ben-jacobson/bench_psu/IO.sch

## KiCad design IO.sch (2021-01-01)

Schematic: IO.sch

Parts:
C8, C13, C14, C16: 0.1uF
C9, C10, C11, C12: 1uF
R4, R5, R6, R7, R8, R11: 10K
R9, R10: 1K
SW2: CH1_Vadj
SW3: CH2_Vadj
U5: 74HC14
U7: 4013

Notes on the sheet:
CH1 Voltage Adjustment - Rotary Encoder
CH2 Voltage Adjustment - Rotary Encoder
