ben-jacobson/bench_psu/MCU.sch

## KiCad design MCU.sch (2021-01-09)

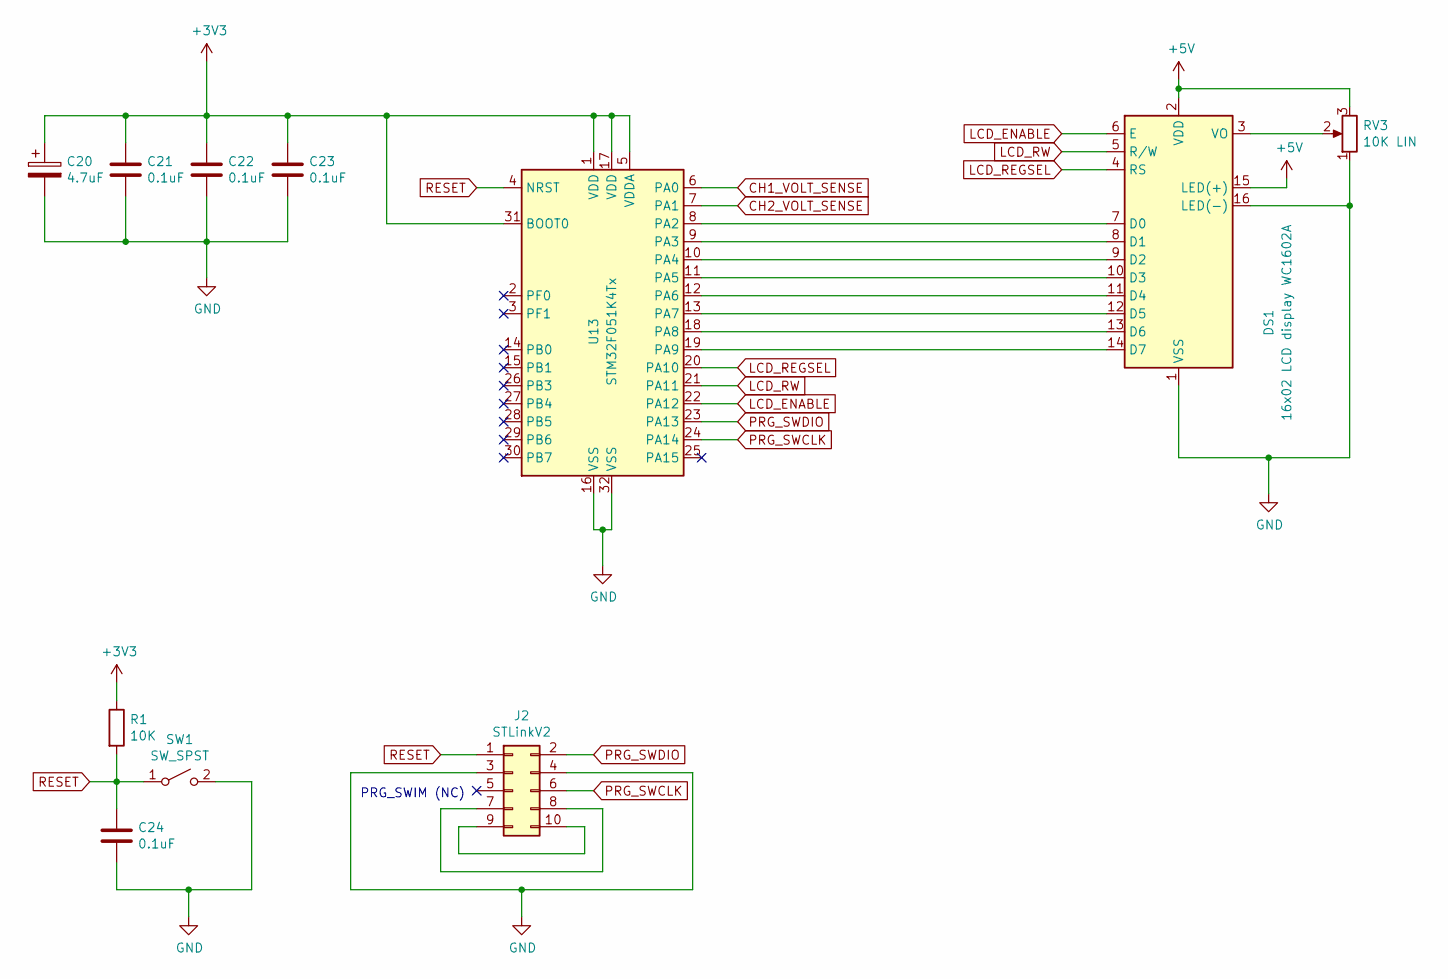
[picture p3: schematic MCU.sch]

Parts:
C20: 4.7uF
C21, C22, C23, C24: 0.1uF
DS1: 16x02 LCD display WC1602A; WC1602A
J2: STLinkV2; PinHeader_2x05_P2.54mm_Vertical
R1: 10K
RV3: 10K LIN
SW1: SW_SPST
U13: STM32F051K4Tx; LQFP-32_7x7mm_P0.8mm

Connections:
+3V3: C20.1, C21.1, C22.1, C23.1, R1.1, U13.1 (VDD), U13.5 (VDDA), U13.17 (VDD), U13.31 (BOOT0)
+5V: DS1.2 (VDD), DS1.15 (LED(+)), RV3.3
CH1_VOLT_SENSE: U13.6 (PA0)
CH2_VOLT_SENSE: U13.7 (PA1)
GND: C20.2, C21.2, C22.2, C23.2, C24.2, DS1.1 (VSS), DS1.16 (LED(-)), J2.3, J2.4, RV3.1, SW1.2 (B), U13.16 (VSS), U13.32 (VSS)
LCD_ENABLE: DS1.6 (E), U13.22 (PA12)
LCD_REGSEL: DS1.4 (RS), U13.20 (PA10)
LCD_RW: DS1.5 (R/W), U13.21 (PA11)
unnamed: DS1.3 (VO), RV3.2
unnamed: DS1.7 (D0), U13.8 (PA2)
unnamed: DS1.8 (D1), U13.9 (PA3)
unnamed: DS1.9 (D2), U13.10 (PA4)
unnamed: DS1.10 (D3), U13.11 (PA5)
unnamed: DS1.11 (D4), U13.12 (PA6)
unnamed: DS1.12 (D5), U13.13 (PA7)
unnamed: DS1.13 (D6), U13.18 (PA8)
unnamed: DS1.14 (D7), U13.19 (PA9)
unnamed: J2.7, J2.8
unnamed: J2.9, J2.10
PRG_SWCLK: J2.6, U13.24 (PA14)
PRG_SWDIO: J2.2, U13.23 (PA13)
RESET: C24.1, J2.1, R1.2, SW1.1 (A), U13.4 (NRST)

Notes on the sheet:
PRG_SWIM (NC)
