ben-jacobson/bench_psu/PSUs.sch

## KiCad design PSUs.sch (2021-01-24)

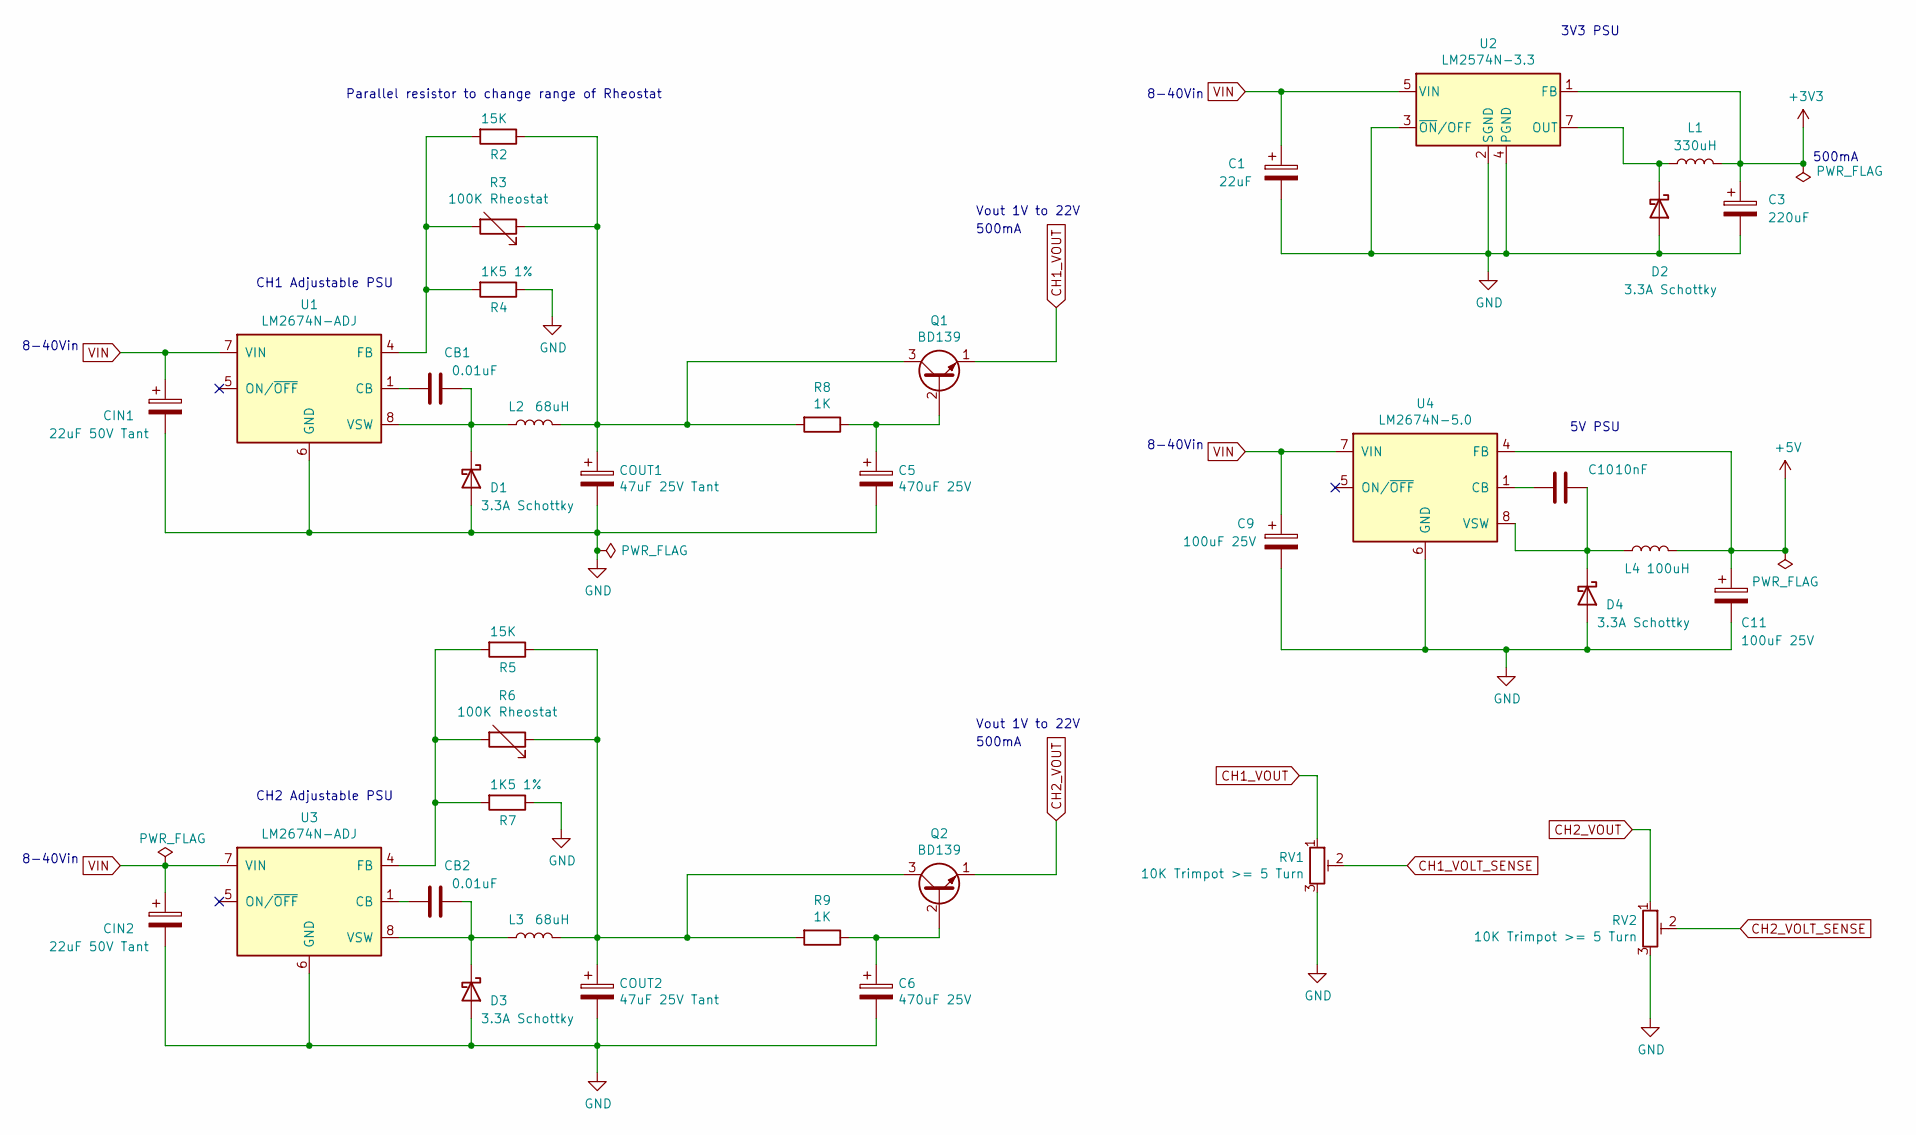
[picture p4: schematic PSUs.sch]

Parts:
C1: 22uF
C3: 220uF
C5, C6: 470uF 25V
C9, C11: 100uF 25V
C10: 10nF
CB1, CB2: 0.01uF
CIN1, CIN2: 22uF 50V Tant
COUT1, COUT2: 47uF 25V Tant
D1, D2, D3, D4: 3.3A Schottky
L1: 330uH
L2, L3: 68uH
L4: 100uH
Q1, Q2: BD139; TO-39-3
R2, R5: 15K
R3, R6: 100K Rheostat
R4, R7: 1K5 1%
R8, R9: 1K
RV1, RV2: 10K Trimpot >= 5 Turn
U1, U3: LM2674N-ADJ
U2: LM2574N-3.3
U4: LM2674N-5.0; DIP-8_W7.62mm

Connections:
+3V3: C1.1, C3.1, C9.1, CIN1.1, CIN2.1, L1.2, U1.7 (VIN), U2.1 (FB), U2.5 (VIN), U3.7 (VIN), U4.7 (VIN)
+5V: C11.1, L4.2, U4.4 (FB)
CH1_VOLT_SENSE: RV1.2
CH1_VOUT: Q1.1 (E), RV1.1
CH2_VOLT_SENSE: RV2.2
CH2_VOUT: Q2.1 (E), RV2.1
GND: C1.2, C3.2, C5.2, C6.2, C9.2, C11.2, CIN1.2, CIN2.2, COUT1.2, COUT2.2, D1.2 (A), D2.2 (A), D3.2 (A), D4.2 (A), R4.1, R7.1, RV1.3, RV2.3, U1.6 (GND), U2.2 (SGND), U2.3 (~ON~/OFF), U2.4 (PGND), U3.6 (GND), U4.6 (GND)
unnamed: C5.1, Q1.2 (B), R8.1
unnamed: C6.1, Q2.2 (B), R9.1
unnamed: C10.1, D4.1 (K), L4.1, U4.8 (VSW)
unnamed: C10.2, U4.1 (CB)
unnamed: CB1.1, U1.1 (CB)
unnamed: CB1.2, D1.1 (K), L2.1, U1.8 (VSW)
unnamed: CB2.1, U3.1 (CB)
unnamed: CB2.2, D3.1 (K), L3.1, U3.8 (VSW)
unnamed: COUT1.1, L2.2, Q1.3 (C), R2.1, R3.1, R8.2
unnamed: COUT2.1, L3.2, Q2.3 (C), R5.1, R6.1, R9.2
unnamed: D2.1 (K), L1.1, U2.7 (OUT)
unnamed: R2.2, R3.2, R4.2, U1.4 (FB)
unnamed: R5.2, R6.2, R7.2, U3.4 (FB)

Notes on the sheet:
Vout 1V to 22V
500mA
8-40Vin
CH2 Adjustable PSU
CH1 Adjustable PSU
3V3 PSU
Parallel resistor to change range of Rheostat
5V PSU
